ampnics/IoT_Based_Air_Quality_Monitoring_System/Air_Quality_Monitor/Docs/img_2.png

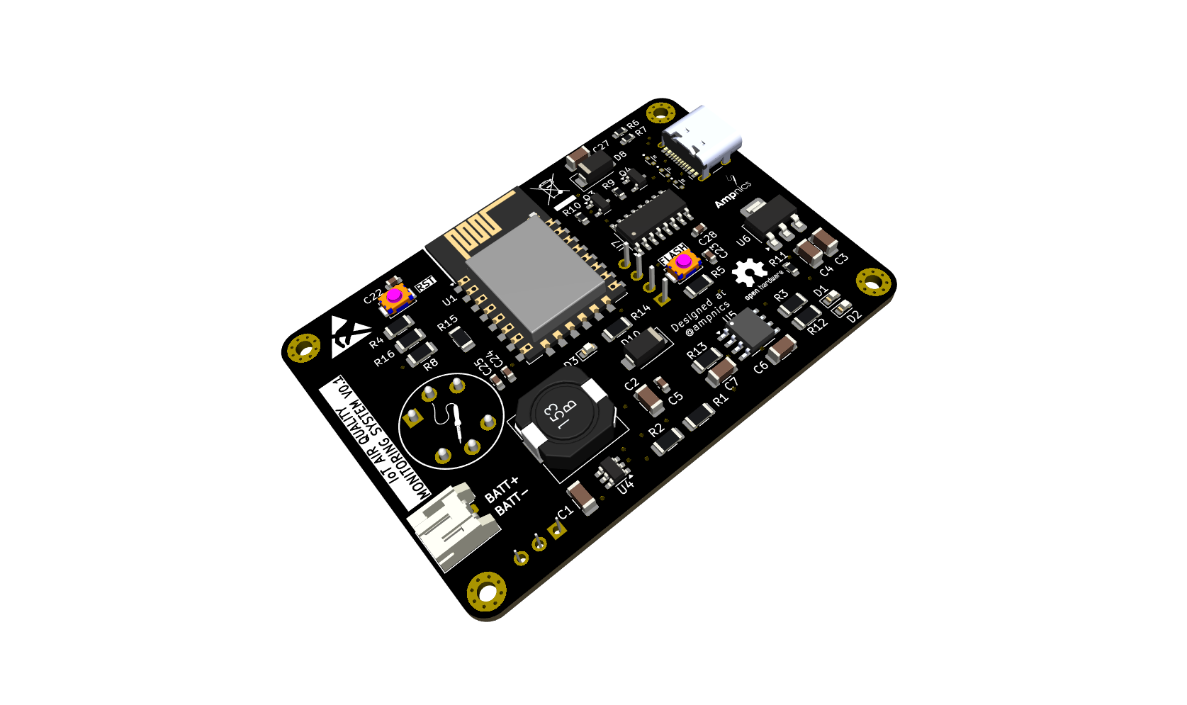
Air_Quality_Monitor/Docs/img_2.png
