ampnics/IoT_Based_Air_Quality_Monitoring_System/Air_Quality_Monitor/External 3d model/mq-8-gas-sensor-1.snapshot.1/MQ-8 gas sensor H2.jpg

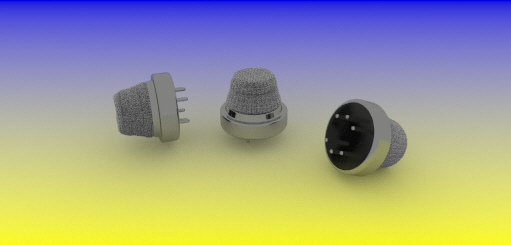
Air_Quality_Monitor/External 3d model/mq-8-gas-sensor-1.snapshot.1/MQ-8 gas sensor H2.jpg
